TehoorMarjan/calendarhouse/Design/IMG_20241116_183329.jpg

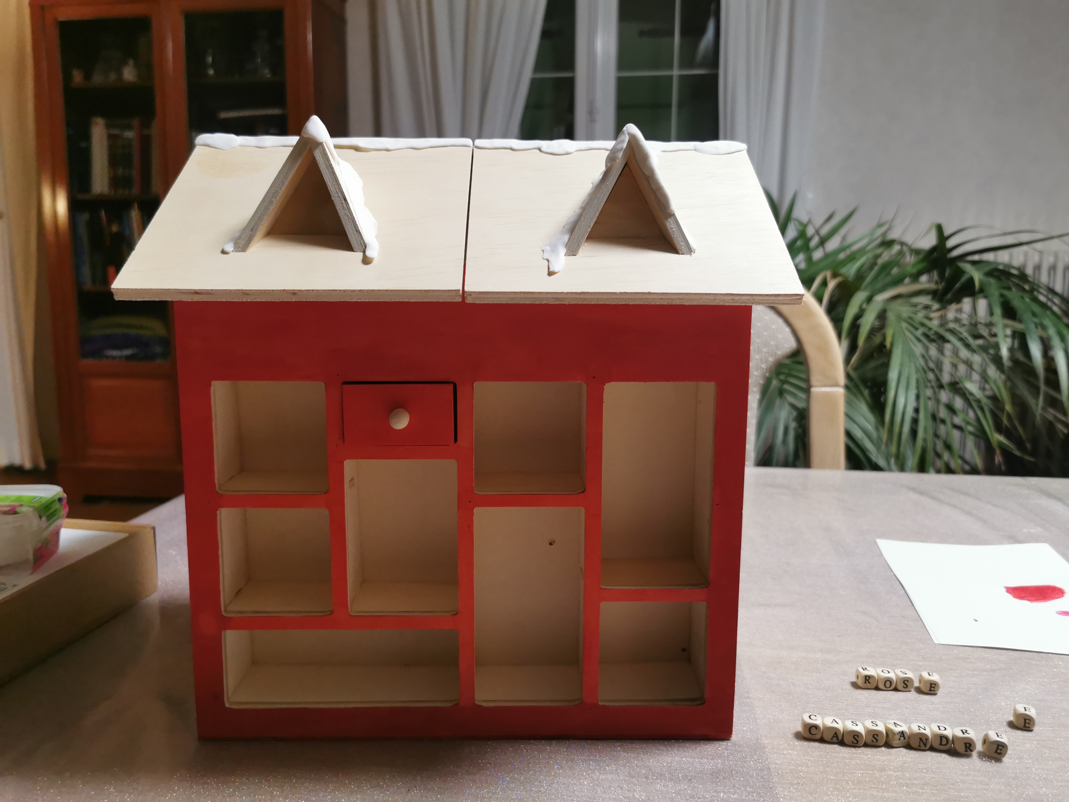
Design/IMG_20241116_183329.jpg
