TehoorMarjan/calendarhouse/Design/IMG_20241116_183344.jpg

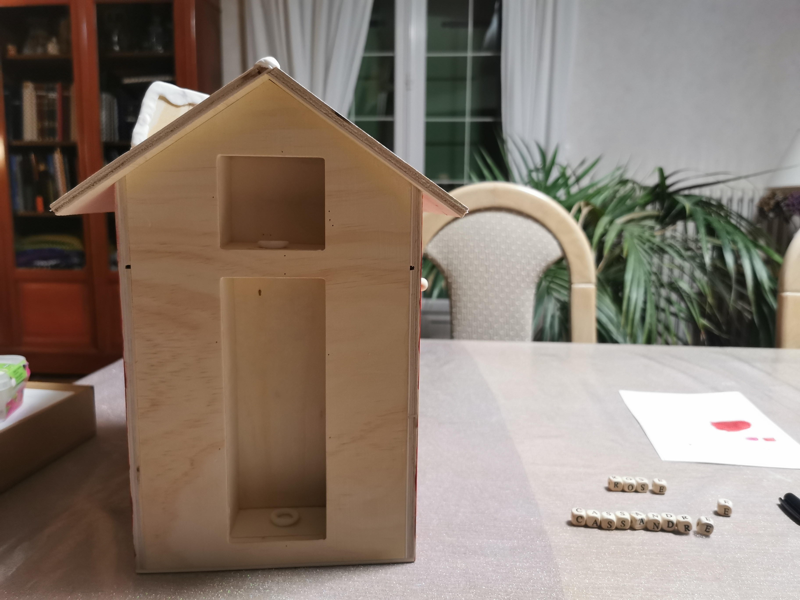
Design/IMG_20241116_183344.jpg
